Maretzky85/Mitsu1GReader/src/lcd.cpp

#include <lcd.h>

hd44780_I2Cexp lcd;

const int rps_x_position = LCD_COLS - 2;
const int rps_y_position = 0;
const int printSize = LCD_COLS - 2;
bool redraw = false;

char headerBuffer[printSize + 1];
char resultBuffer0[printSize - 2];
char resultBuffer1[printSize - 2];
char resultBuffer2[printSize - 2];
char * resultBuffers[] = {
        resultBuffer0,
        resultBuffer1,
        resultBuffer2
};

char rpsBuffer[3];

char temp[LCD_COLS - 1];
char headerFormat[6];
char resultFormat[6];

//display optimisation - dont print if same
const char *lastPrintedStatus = nullptr;
const char *lastPrintedHeader = nullptr;
const char *lastPrintedResultsName[] = {
        nullptr,
        nullptr,
        nullptr
};
char lastResultPrinted[LCD_COLS] = "";
char lastResults[3][LCD_COLS] = {"", "", ""};
int lastRpsPrinted = -1;
int lastDTCIdPrinted = -1;

//const byte star[] PROGMEM = {
//        B00100,
//        B00100,
//        B10001,
//        B01010,
//        B00100,
//        B01010,
//        B10101,
//        B00100
//};

void lcdStart() {
    sprintf(headerFormat, "%s%d%s", "%-", LCD_COLS - 4, "s");
    sprintf(resultFormat, "%s%d%s", "%-", LCD_COLS - 5, "s");
    lcd.begin(LCD_COLS, LCD_ROWS);
    lcd.backlight();
//    lcd.createChar(0, star);
//    lcd.write(0);
}

void printRps(int requestPerSecond) {
    if (requestPerSecond != lastRpsPrinted || redraw) {
        sprintf(rpsBuffer, "%-2d", requestPerSecond);
        lcd.setCursor(rps_x_position, rps_y_position);
        lcd.print(rpsBuffer);
        lastRpsPrinted = requestPerSecond;
    }
}

void printHeader(char *header) {
    if (lastPrintedHeader != header || redraw) {
        snprintf(headerBuffer, printSize, headerFormat, header);
        lcd.setCursor(0, 0);
        lcd.print(headerBuffer);
        lastPrintedHeader = header;
    }
}

void printHeader(const char *header) {
    if (lastPrintedHeader != header || redraw) {
        strcpy_P(temp, header);
        snprintf(headerBuffer, printSize, headerFormat, temp);
        lcd.setCursor(0, 0);
        lcd.print(headerBuffer);
        lastPrintedHeader = header;
    }
}

void printResult(char *result, boolean force) {
    if (strcmp(lastResultPrinted, result) != 0 || force || redraw) {
        strncpy(lastResultPrinted, result, sizeof(lastResultPrinted) - 1);
        lastResultPrinted[sizeof(lastResultPrinted) - 1] = '\0';
        sprintf(resultBuffer0, resultFormat, result);
        lcd.setCursor(0, 1);
        lcd.print(resultBuffer0);
    }
}

void printResultName(const char *name, int row) {
    if (lastPrintedResultsName[row] != name || redraw) {
        strcpy_P(temp, name);
        sprintf(resultBuffers[row], resultFormat , temp);
        lcd.setCursor(0, row + 1);
        lcd.print(resultBuffers[row]);
        lastPrintedResultsName[row] = name;
    }
}

void printResult(char *result, int row, int rOffset) {
    if (strcmp(lastResults[row], result) != 0 || redraw) {
        strncpy(lastResults[row], result, sizeof(lastResults[row]) - 1);
        lastResults[row][sizeof(lastResults[row]) - 1] = '\0';
        lcd.setCursor(LCD_COLS - 8 + rOffset, row + 1);
        lcd.print(result);
    }
}

void printResult(const char *result, int row) {
    char temp[4];
    char resBuffer[4];
    strcpy_P(temp, result);
    sprintf(resBuffer, "%3s", temp);
    printResult(resBuffer, row, 3);
}

void printResult(int result) {
    sprintf(temp, "%d", result);
    printResult(temp);
}

void printFullRow(int row, const char *text) {
    // Manual pad — avr-libc's minimal printf (default in some builds) does
    // not support the '*' width specifier, so "%-*s" silently produces an
    // empty string. Build the padded buffer by hand instead.
    char buf[LCD_COLS + 1];
    uint8_t i = 0;
    while (i < LCD_COLS && text[i]) {
        buf[i] = text[i];
        i++;
    }
    while (i < LCD_COLS) {
        buf[i++] = ' ';
    }
    buf[LCD_COLS] = '\0';
    lcd.setCursor(0, row);
    lcd.print(buf);
}

void printResult_P(const char *result) {
    strcpy_P(temp, result);
    printResult(temp);
}

void printDTC(int dtcCode, char dtcName[]) {
    if (lastDTCIdPrinted != dtcCode || redraw) {
        sprintf(resultBuffer0, "%2d - %-8s", dtcCode, dtcName);
        lastDTCIdPrinted = dtcCode;
        lcd.setCursor(0, 1);
    }
    printResult(resultBuffer0);
}

void printDTC(int dtcCode, const char *dtcName, int row) {
    if (lastPrintedResultsName[row] != dtcName || redraw) {
        strcpy_P(temp, dtcName);
        lastDTCIdPrinted = dtcCode;

        sprintf(resultBuffers[row], "%2d - %-10s" , dtcCode, temp);
        lcd.setCursor(0, row + 1);
        lcd.print(resultBuffers[row]);
        lastPrintedResultsName[row] = dtcName;
    }
}

void printError(const char *errorName) {
    strcpy_P(temp, errorName);
    sprintf(resultBuffer0, "%-13s", temp);
    printResult(resultBuffer0);
}

void printDtcCount(int count) {
    lcd.setCursor(LCD_COLS - 2, LCD_ROWS);
    lcd.print(count);
    lcd.print(' ');
}

void printStatus(const char *status){
    if (lastPrintedStatus != status || redraw) {
        char buffer[3];
        lcd.setCursor(LCD_COLS - 4, 0);
        strcpy_P(buffer, status);
        lcd.print(buffer);
        lastPrintedStatus = status;
    }
}

void clearScreen() {
    lcd.clear();
    // Invalidate all dedup state: after lcd.clear() the screen is blank, so
    // the "last printed" caches no longer match what's on the display and
    // any next print of the same content would be wrongly skipped.
    lastPrintedHeader = nullptr;
    lastPrintedStatus = nullptr;
    for (uint8_t i = 0; i < 3; i++) {
        lastPrintedResultsName[i] = nullptr;
        lastResults[i][0] = '\0';
    }
    lastResultPrinted[0] = '\0';
    lastRpsPrinted = -1;
    lastDTCIdPrinted = -1;
}
