Maretzky85/Mitsu1GReader/src/lcd.h

#pragma once

#include <Arduino.h>
#include <Wire.h>
#include <hd44780.h>
#include <hd44780ioClass/hd44780_I2Cexp.h>

#define LCD_COLS 20
#define LCD_ROWS 4

extern bool redraw;

void lcdStart();

void printRps(int requestPerSecond);

void printHeader(char *header);

void printHeader(const char *header);

void printError(const char *errorName);

void printDTC(int dtcCode, char *dtcName);

void printResult(char *result, boolean force = false);

void printResult_P(const char *result);

void printResult(int result);

void printDtcCount(int count);

void clearScreen();

void printStatus(const char *status);
//LCD 4 rows

void printResult(char *result, int row, int rOffset = 0);

void printResult(const char *result, int row);

// Write text at column 0 of the given LCD row (0-indexed), padded/clipped
// to LCD_COLS. Bypasses the dedup buffers used by printResult() and
// printResultName() so it's safe for arbitrary rows including the header.
void printFullRow(int row, const char *text);

void printResultName(const char *name, int row);

void printDTC(int dtcCode, const char *dtcName, int row);
